c3ko/SecondFactorKeypad/images/Case_Amazon.PNG

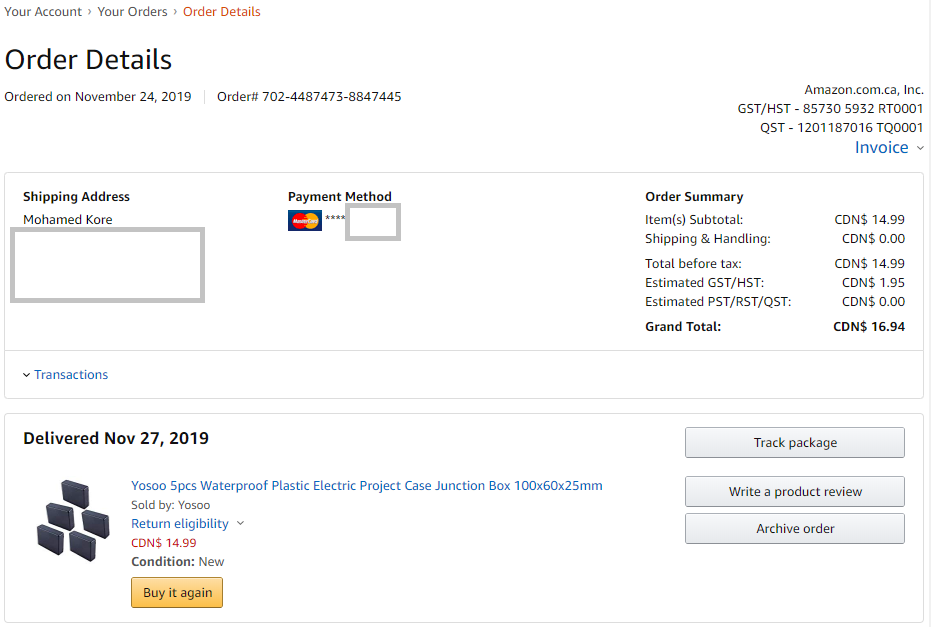
images/Case_Amazon.PNG
