c3ko/SecondFactorKeypad/images/checkout.PNG

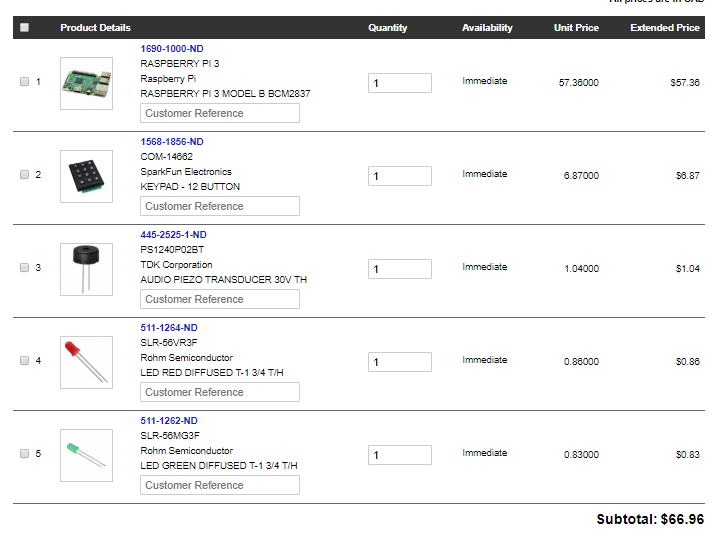
images/checkout.PNG
