c3ko/SecondFactorKeypad/images/Keypad-rear.jpg

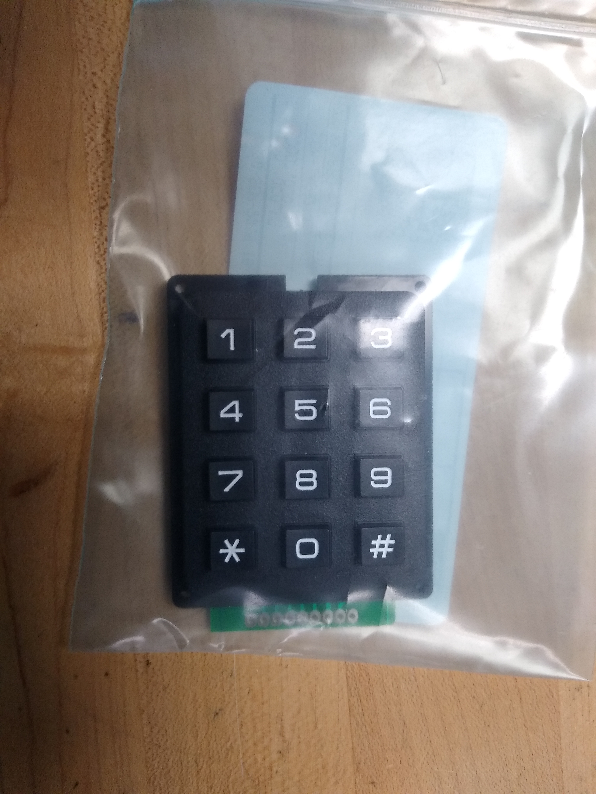
images/Keypad-rear.jpg
