c3ko/SecondFactorKeypad/images/Nucleo-Rear.jpg

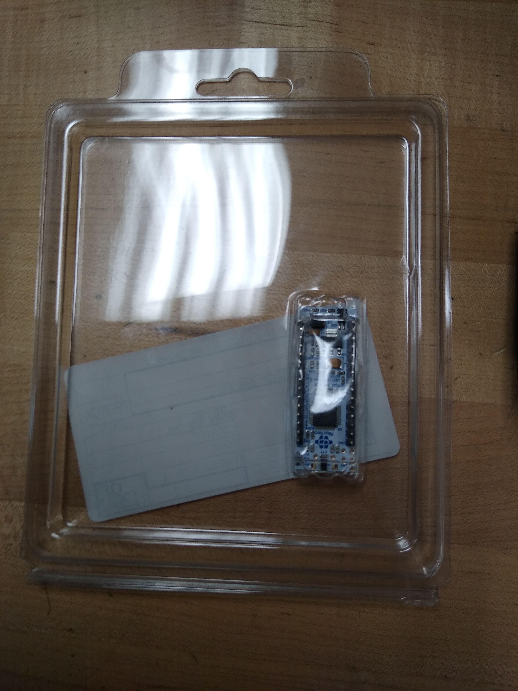
images/Nucleo-Rear.jpg
